Nomados/Meteorology-Station/gfxconf.h

/*
 * Copyright (c) 2012, 2013, Joel Bodenmann aka Tectu <joel@unormal.org>
 * Copyright (c) 2012, 2013, Andrew Hannam aka inmarket
 *
 * All rights reserved.
 *
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
 * THIS SOFTWARE IS PROVIDED BY THE COPYRIGHT HOLDERS AND CONTRIBUTORS "AS IS" AND
 * ANY EXPRESS OR IMPLIED WARRANTIES, INCLUDING, BUT NOT LIMITED TO, THE IMPLIED
 * WARRANTIES OF MERCHANTABILITY AND FITNESS FOR A PARTICULAR PURPOSE ARE
 * DISCLAIMED. IN NO EVENT SHALL <COPYRIGHT HOLDER> BE LIABLE FOR ANY
 * DIRECT, INDIRECT, INCIDENTAL, SPECIAL, EXEMPLARY, OR CONSEQUENTIAL DAMAGES
 * (INCLUDING, BUT NOT LIMITED TO, PROCUREMENT OF SUBSTITUTE GOODS OR SERVICES;
 * LOSS OF USE, DATA, OR PROFITS; OR BUSINESS INTERRUPTION) HOWEVER CAUSED AND
 * ON ANY THEORY OF LIABILITY, WHETHER IN CONTRACT, STRICT LIABILITY, OR TORT
 * (INCLUDING NEGLIGENCE OR OTHERWISE) ARISING IN ANY WAY OUT OF THE USE OF THIS
 * SOFTWARE, EVEN IF ADVISED OF THE POSSIBILITY OF SUCH DAMAGE.
 */

#ifndef _GFXCONF_H
#define _GFXCONF_H

/* The operating system to use. One of these must be defined - preferably in your Makefile */
#define GFX_USE_OS_CHIBIOS		TRUE
//#define GFX_USE_OS_WIN32		FALSE
//#define GFX_USE_OS_LINUX		FALSE
//#define GFX_USE_OS_OSX		FALSE

/* GFX sub-systems to turn on */
#define GFX_USE_GDISP			TRUE
#define GDISP_NEED_MULTITHREAD TRUE
/* Features for the GDISP sub-system. */
#define GDISP_NEED_VALIDATION	FALSE
/* Features for the GDISP sub-system. */
#define GDISP_NEED_CLIP				TRUE
#define GDISP_NEED_TEXT				TRUE
#define GDISP_NEED_CIRCLE			TRUE
#define GDISP_NEED_ELLIPSE			FALSE
#define GDISP_NEED_ARC				FALSE
#define GDISP_NEED_CONVEX_POLYGON	FALSE
#define GDISP_NEED_SCROLL			FALSE
#define GDISP_NEED_PIXELREAD		FALSE
#define GDISP_NEED_ASYNC			FALSE
#define GDISP_NEED_MSGAPI			FALSE


/* Build in Fonts */
#define GDISP_INCLUDE_FONT_SMALL		FALSE
#define GDISP_INCLUDE_FONT_LARGER		FALSE
#define GDISP_INCLUDE_FONT_UI1			TRUE
#define GDISP_INCLUDE_FONT_UI2			TRUE
#define GDISP_INCLUDE_FONT_LARGENUMBERS	TRUE

#define SSD1306_SH1106 TRUE

#endif /* _GFXCONF_H */
